wjossowski/tinkerpad-pcb/3dmodel/m2_screws/m2_nut v1.stl

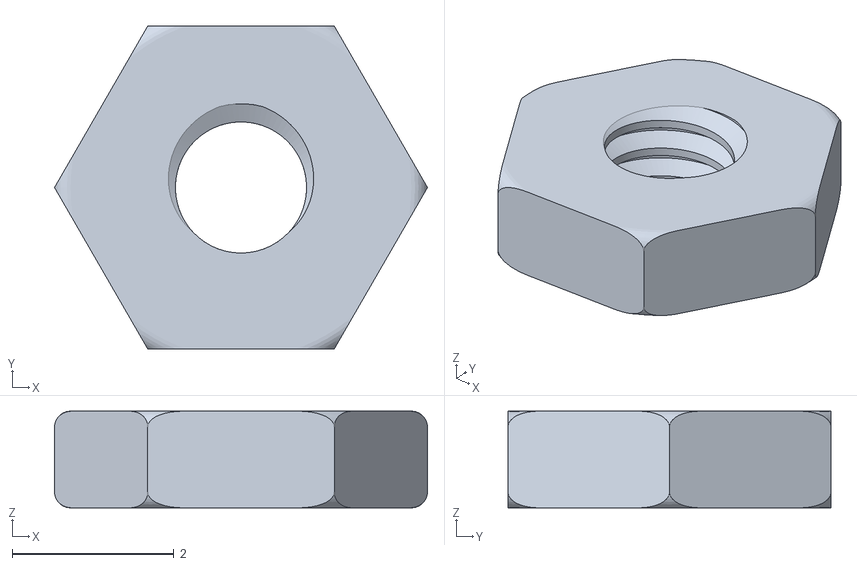
[picture p15: CAD file, 2023-05-01]
3dmodel/m2_screws/m2_nut v1.stl
4.62 x 4.00 x 1.20
