wjossowski/tinkerpad-pcb/3dmodel/m2_screws/M2x6 v1.stl

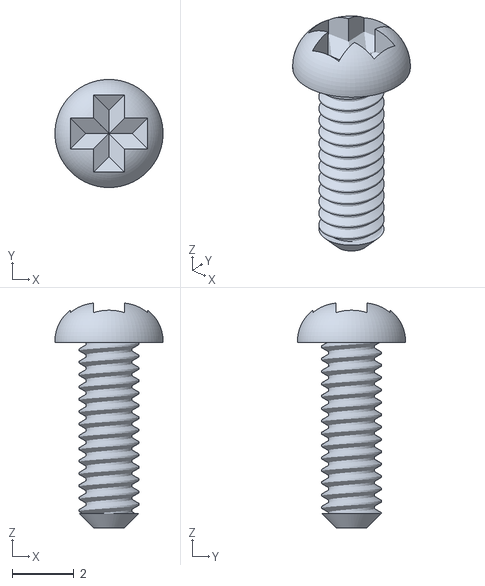
[picture p16: CAD file, 2023-05-01]
3dmodel/m2_screws/M2x6 v1.stl
3.50 x 3.50 x 7.28
