wjossowski/tinkerpad-pcb/3dmodel/m2_screws/M2Sx15 v1.stl

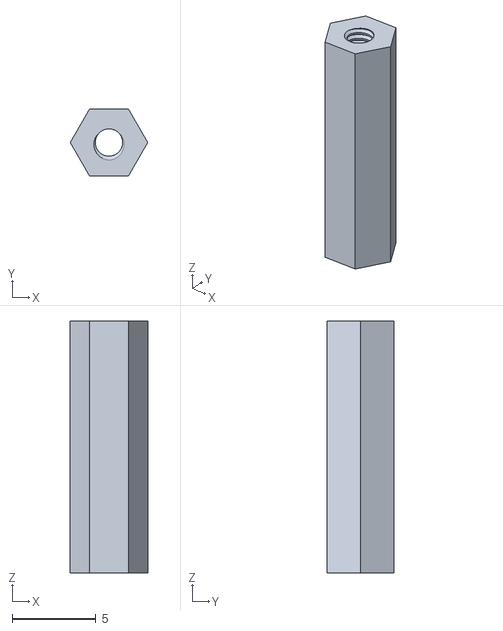
[picture p18: CAD file, 2023-05-01]
3dmodel/m2_screws/M2Sx15 v1.stl
4.62 x 4.00 x 15.0
